schilkp/PmodADC/Doc/imgs/v0.0_testing.jpg

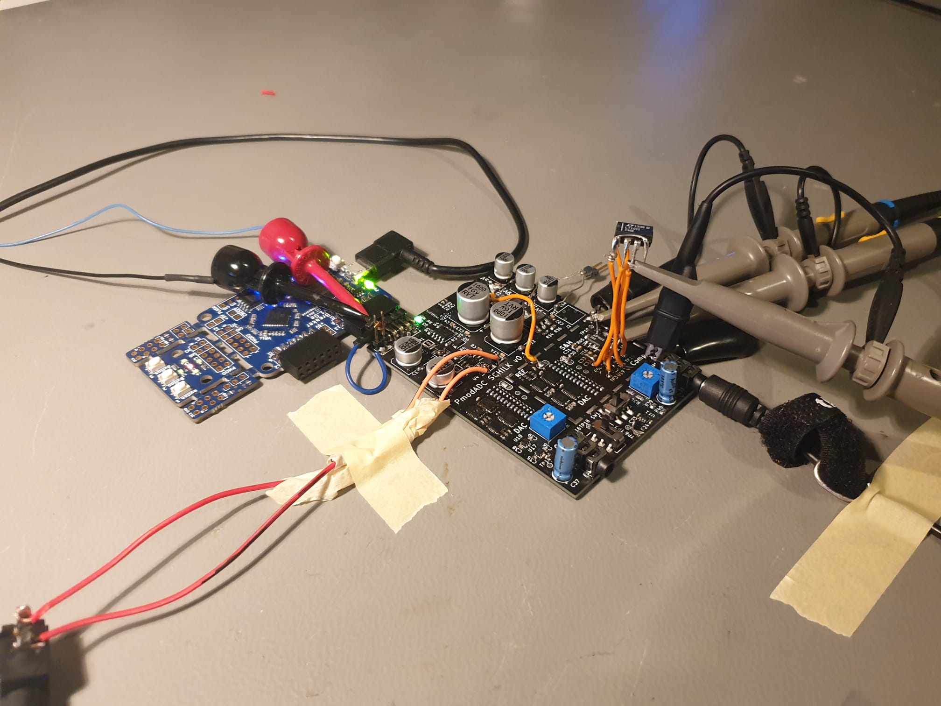
Doc/imgs/v0.0_testing.jpg
