schilkp/PmodADC/Simulations/AudioOutput.asc

C1: cap; 10µ
C2: cap; 4.7n
C3: cap; 10n
C4: cap; 4.7n
C5: cap; 10n
R1: res; {50k*(1-P)}
R2: res; 1.2k
R3: res; 1.2k
R4: res; {50k*P}
R5: res; 1.2k
R6: res; 1.2k
U1: OP07
U2: OP07
U3: OP07
U4: OP07
V1: voltage; 9V
V2: voltage; 5V
V3: voltage; SINE(2.5V 2.5V 10000); AC 0.7
V4: voltage; 5V
Named nets: 0, +9V, +5V, -5V
.ac oct 20 1 100000
;tran 0.01
.param P=0.001
20kHz Sallen-Key LP
20kHz Sallen-Key LP
Input Buffer
Variable Buffer
Buffer
