schilkp/PmodADC/Simulations/AudioInput.asc

C2: cap; 4.7n
C3: cap; 10n
C4: cap; 10µ
R2: res; 20.5k
R3: res; 20.5k
R4: res; 1.2k
R5: res; 1.2k
R6: res; 50k
R7: res; 5k
U1: OP07
U2: OP07
V1: voltage; 9V
V2: voltage; 5V
V3: voltage; ""; AC 0.7
V4: voltage; 5V
Named nets: 0, +9V, +5V, -5V, S&H
.ac oct 20 1 100000
;tran 0.001
AC Coupling
Input Buffer
Variable Amplification
20kHz Sallen-Key LP
Biasing
50k Var. R. allows
for x1 - x11 gain
